F3lda/BP-HistoR/src/BP_M1/I2Saudio/I2Saudio.ino

//**********************************************************************************************************
//*    audioI2S-- I2S audiodecoder for ESP32,                                                              *
//**********************************************************************************************************
//
// first release on 11/2018
// Version 3  , Jul.02/2020
//
//
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

#include "Arduino.h"
#include "WiFiMulti.h"
#include "Audio.h"
//#include "SPI.h"
//#include "SD.h"
//#include "FS.h"

// Digital I/O used
#define SD_CS          5
#define SPI_MOSI      23
#define SPI_MISO      19
#define SPI_SCK       18

#define I2S_DOUT      22
#define I2S_BCLK      26
#define I2S_LRC       25

Audio audio;
WiFiMulti wifiMulti;
String ssid =     "DodikovyInternety";
String password = "dodikovachyse84";


void setup() {
    pinMode(SD_CS, OUTPUT);
    digitalWrite(SD_CS, HIGH);
    SPI.begin(SPI_SCK, SPI_MISO, SPI_MOSI);
    SPI.setFrequency(1000000);

    
    Serial.begin(115200);
    while(!Serial);
    
    SD.begin(SD_CS);
    WiFi.mode(WIFI_STA);
    wifiMulti.addAP(ssid.c_str(), password.c_str());
    wifiMulti.run();
    if(WiFi.status() != WL_CONNECTED){
        WiFi.disconnect(true);
        wifiMulti.run();
    }
    audio.setPinout(I2S_BCLK, I2S_LRC, I2S_DOUT);
    audio.setVolume(12); // 0...21

    audio.connecttoFS(SD, "/DqnceRemix/50 Cent - Candy Shop 2k23 (KROB Pump Up edit).mp3");
//    audio.connecttohost("http://www.wdr.de/wdrlive/media/einslive.m3u");
//    audio.connecttohost("http://somafm.com/wma128/missioncontrol.asx"); //  asx
//    audio.connecttohost("http://mp3.ffh.de/radioffh/hqlivestream.aac"); //  128k aac
      //audio.connecttohost("http://mp3.ffh.de/radioffh/hqlivestream.mp3"); //  128k mp3
      //audio.connecttohost("https://ice5.abradio.cz/hitvysocina128.mp3");
      
}

void loop()
{
    audio.loop();
    if(Serial.available()){ // put streamURL in serial monitor
        audio.stopSong();
        String r=Serial.readString(); r.trim();
        if(r.length()>5) audio.connecttoFS(SD, r.c_str());//audio.connecttohost(r.c_str());
        log_i("free heap=%i", ESP.getFreeHeap());
    }
}

// optional
void audio_info(const char *info){
    Serial.print("info        "); Serial.println(info);
}
void audio_id3data(const char *info){  //id3 metadata
    Serial.print("id3data     ");Serial.println(info);
}
void audio_eof_mp3(const char *info){  //end of file
    Serial.print("eof_mp3     ");Serial.println(info);
}
void audio_showstation(const char *info){
    Serial.print("station     ");Serial.println(info);
}
void audio_showstreamtitle(const char *info){
    Serial.print("streamtitle ");Serial.println(info);
}
void audio_bitrate(const char *info){
    Serial.print("bitrate     ");Serial.println(info);
}
void audio_commercial(const char *info){  //duration in sec
    Serial.print("commercial  ");Serial.println(info);
}
void audio_icyurl(const char *info){  //homepage
    Serial.print("icyurl      ");Serial.println(info);
}
void audio_lasthost(const char *info){  //stream URL played
    Serial.print("lasthost    ");Serial.println(info);
}
