F3lda/BP-HistoR/src/BP_AM/BP_AM.ino

/*
 * si5351_example.ino - Simple example of using Si5351Arduino library
 *
 * Copyright (C) 2015 - 2016 Jason Milldrum <milldrum@gmail.com>
 *
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
 * You should have received a copy of the GNU General Public License
 * along with this program.  If not, see <http://www.gnu.org/licenses/>.
 */
//https://github.com/etherkit/Si5351Arduino
#include "si5351.h"
#include "Wire.h"

Si5351 si5351;

#define RELAYPIN 3

void setup()
{
  pinMode(RELAYPIN, OUTPUT);
  digitalWrite(RELAYPIN, LOW);
  
  bool i2c_found; // UNO SDA/A4  SCL/A5

  // Start serial and initialize the Si5351
  Serial.begin(9600);
  i2c_found = si5351.init(SI5351_CRYSTAL_LOAD_8PF, 0, 0);
  if(!i2c_found)
  {
    Serial.println("Device not found on I2C bus!");
  }

  // Set CLK0 to output 10 MHz
  si5351.set_freq(1000000000ULL, SI5351_CLK0);
  si5351.drive_strength(SI5351_CLK0, SI5351_DRIVE_8MA);
  si5351.output_enable(SI5351_CLK0, 1);

  // Set CLK1 to output 175 MHz
  //si5351.set_ms_source(SI5351_CLK1, SI5351_PLLB);
  //si5351.set_freq_manual(17500000000ULL, 70000000000ULL, SI5351_CLK1);

  // Query a status update and wait a bit to let the Si5351 populate the
  // status flags correctly.
  si5351.update_status();
  delay(500);
}

void loop()
{
  // Read the Status Register and print it every 10 seconds
  // cca SYS_INIT: 0  LOL_A: 0  LOL_B: 0  LOS: 0  REVID: 3
  si5351.update_status();
  Serial.print("SYS_INIT: ");
  Serial.print(si5351.dev_status.SYS_INIT);
  Serial.print("  LOL_A: ");
  Serial.print(si5351.dev_status.LOL_A);
  Serial.print("  LOL_B: ");
  Serial.print(si5351.dev_status.LOL_B);
  Serial.print("  LOS: ");
  Serial.print(si5351.dev_status.LOS);
  Serial.print("  REVID: ");
  Serial.println(si5351.dev_status.REVID);

  delay(10000);
}
